phoezelle/puddingplayer/src/ofApp.cpp

#include "ofApp.h"
#include "wiringPi.h"
#include <wiringPiSPI.h>
#include <cstdlib>
#include <iostream>
#include <sstream>
#include <string>
#include <unistd.h>



void ofApp::log(string log,int level,bool color){
  if(level<=loglevel){
    if(color) cout << "\033[32m";
    if(level==WARNING) cout << "\x1b[31m";
    cout << log;
    if(color || level==WARNING) cout << "\x1b[0m";
    cout << endl;
    if(level<=USR)firstMessage+=log+"\n";
  }
}



void ofApp::definePlateform(){
  ofTargetPlatform myRun = ofGetTargetPlatform();
  if (myRun==OF_TARGET_LINUXARMV7L || myRun==OF_TARGET_LINUXARMV6L){
    pi=true;
    fingerMovie->setPixelFormat(OF_PIXELS_NATIVE);
    fingerMovie2->setPixelFormat(OF_PIXELS_NATIVE);
    rootDirectory="/tmp/stick";
    log("RASPI DETECT path from usb stick", USR);
    
  } else {
    pi=false;
    rootDirectory="";
    log("MAC DETECT", USR);
    
  }
}

void ofApp::usbstickMount(){
  ofDirectory myDir;
  if(myDir.doesDirectoryExist(rootDirectory)){
  } else {
    ofSystem("sudo mkdir "+rootDirectory);
    log("create mountpoint "+rootDirectory, USR);
  }
  if (myDir.listDir(rootDirectory)>1) {
    log("USB stick already mount", USR);
    flash_ledG(1);
  } else {
    ofSystem("sudo mount -o rw /dev/sda1 "+rootDirectory);
    if(myDir.listDir(rootDirectory)>1) {
      log("mount usb stick", USR);
      flash_ledG(1);
    }else {
      log("problem for mounting usb stick", WARNING);
      flash_ledR(1);
    }
  }
  rootDirectory+="/";
}



//--------------------------------------------------------------
void ofApp::setup(){
  
  ledG_value = 0;
  ledG_state = 0;
  ledG_time_on = ofGetElapsedTimeMillis();
  ledG_time_period = 50;
  
  ledR_state = 0;
  ledR_value = 0;
  ledR_time_on = ofGetElapsedTimeMillis();
  ledR_time_period = 200;
  
  nvideo=0;
  gochangevideo=0;
  isplayground=true;
  
  
  firstlaunch=true;
  loglevel=USR;
  pi=true;
  currentVideo=-1;
  currentScene=0;
  currentBackground=0;
  
  log("STARTUP",USR,true);
  
  ofHideCursor();
  ofBackground(0,0,0);
	ofSetVerticalSync(true);
  
  fingerMovie = new ofVideoPlayer();
  fingerMovie2 = new ofVideoPlayer();
  
  definePlateform();
  if (pi) {
    usbstickMount();
    initGPIO();
    
    
  }
  ofBackground(0,0,0);
  getPref();
  setcurrentCharacter(0);
  checkNetwork();
  
  thread.startThread(true);
  
  playBackground();
  
	// Uncomment this to show movies with alpha channels
	// fingerMovie.setPixelFormat(OF_PIXELS_RGBA);
  
}


void ofApp::getPref(){
  
  posX=0;
  posY=0;
  width=ofGetScreenWidth();
  height=ofGetScreenHeight();
  log("screen size "+ofToString(ofGetWindowWidth())+" x "+ofToString(ofGetWindowHeight())+" / "+ofToString(ofGetScreenWidth())+" x "+ofToString(ofGetScreenHeight()),USR);
  loglevel=DEBUG;
  
  ofBuffer buffer = ofBufferFromFile(rootDirectory+"config.txt");
	if(buffer.size()) {
    for (ofBuffer::Line it = buffer.getLines().begin(), end = buffer.getLines().end(); it != end; ++it) {
      string line = *it;
      if(line.empty() == false) {
        string attribute = ofTrim(ofSplitString(line, "=")[0]);
        string value = ofTrim(ofSplitString(line, "=")[1]);
        
        if (attribute.compare("positionX")==0) posX=ofToInt(value);
        if (attribute.compare("positionY")==0) posY=ofToInt(value);
        if (attribute.compare("largeur")==0) width=ofToInt(value);
        if (attribute.compare("hauteur")==0) height=ofToInt(value);
        if (attribute.compare("loglevel")==0) loglevel=ofToInt(value);
        if (attribute.compare("dossier_personnage")==0) characterList =  ofSplitString(value, ",");
        if (attribute.compare("dossier_background")==0) backgroundDirectory = value;
        log("read param "+attribute+" = "+value, DEBUG);
      }else {
        break;
      }
    }
	}else{
    log(rootDirectory+"config.txt file not found",WARNING);
    flash_ledR(2);
  }
  
  ofSetWindowShape(width, height);
}


void ofApp::setcurrentCharacter(int _character){
  currentCharacter = _character;
  log("set character n" + ofToString(currentCharacter) + " -> directory " + characterList[currentCharacter], USR);
  buildMediaList();
}


void ofApp::buildMediaList(){
  log("Build media list",USR);
  mediaList.clear();
  ofDirectory myDir;
  if(!myDir.doesDirectoryExist(rootDirectory+"movies")){
    ofSystem("sudo mkdir "+rootDirectory+"movies");
    log("create movies directory", USR,true);
  }
  mediaDirectory = "movies/"+characterList[currentCharacter];
  if(!myDir.doesDirectoryExist(rootDirectory+mediaDirectory)){
    ofSystem("sudo mkdir "+rootDirectory+mediaDirectory);
    log("create " + mediaDirectory + " directory", USR,true);
  }
  ofDirectory mediaDir(rootDirectory+mediaDirectory);
  mediaDir.allowExt("mp4");
  mediaDir.allowExt("mov");
  mediaDir.allowExt("avi");
  nbMedia = mediaDir.listDir();
  mediaDir.sort();
  int lastScene=-1;
  vector <string> scene;
  if (nbMedia>0) {
    log("find " + ofToString(nbMedia) + " movie files in " + mediaDirectory,DEBUG);
    for (int i=0; i<nbMedia; i++) {
      string media = mediaDir.getName(i);
      
      int numScene = ofToInt(ofTrim(ofSplitString(media, "_")[0]));
      if(lastScene == -1) lastScene = numScene;
      int numVideo = ofToInt(ofTrim(ofSplitString(media, "_")[1]));
      if(numScene != lastScene) {
        log("new scene",DEBUG);
        lastScene = numScene;
        mediaList.push_back(scene);
        scene.clear();
      }
      log(media,DEBUG);
      scene.push_back(media);
    }
    mediaList.push_back(scene);
  }else{
    log("no media found in " + mediaDirectory,WARNING);
  }
  
  
  ofDirectory backgroundDir(rootDirectory+mediaDirectory+"/"+backgroundDirectory);
  backgroundDir.allowExt("mp4");
  backgroundDir.allowExt("mov");
  backgroundDir.allowExt("avi");
  int nbBackground = backgroundDir.listDir();
  if (nbBackground>0) {
    log("find " + ofToString(nbBackground) + " background movie files in " + mediaDirectory+"/"+backgroundDirectory,DEBUG);
    for (int i=0; i<nbBackground; i++) {
      string media = backgroundDir.getName(i);
      backgroundList.push_back(media);
    }
  }else{
    log("no background media found in " + mediaDirectory+"/"+backgroundDirectory,WARNING);
  }
}

void ofApp::checkNetwork(){
  cout << "checking network";
  if(pi) {
    string ip_eth = ofTrim(ofSystem("ifconfig eth0 | grep 'inet addr:' | cut -d: -f2 | awk '{ print $1}'"));
    string ip_wlan = ofTrim(ofSystem("ifconfig wlan0 | grep 'inet addr:' | cut -d: -f2 | awk '{ print $1}'"));
    string hostname = ofTrim(ofSystem("cat /etc/hostname"));
    log("network on pi name "+hostname+" : eth "+ip_eth+" ; wlan "+ip_wlan, USR);
  }else {
    string ip_en1 = ofSystem("ifconfig en1 | grep 'inet ' | cut -dt -f2 | awk '{ print $1}'");
    log("network on mac : en1 "+ip_en1, USR);
  }
}


void ofApp::initGPIO(){
  
  pin[0] = PUSH1;
  pin[1] = PUSH2;
  pin[2] = PUSH3;
  
  if(wiringPiSetup() == -1){
    log("Error on wiringPi setup\n",WARNING);
  }else {
    log("configure GPIO IN", USR);
    for (int i=0; i<PIN_NUM; i++) {
      pinMode(pin[i],INPUT);
      pullUpDnControl(pin[i],PUD_DOWN);
      log("read initial state of pin", USR);
      laststate[i]=digitalRead(pin[i]);
    }
    delay(1);
    log("configure GPIO OUT", USR);
    pinMode(LEDR,OUTPUT);
    pinMode(LEDG,OUTPUT);
    
  }
  
  log("wait for RF24 config", USR);
  while (1){
    string input;
    getline(cin, input);
    if(input.length()>3){
      log("cin = "+input, USR);
      if (input.compare("INITEND")==0) break;
    }
  }
  
  
}

void ofApp::getAnalogBattery(){
  
}


void ofApp::playNext(){
  if (currentVideo==-1){
    log("first time play",DEBUG);
    currentVideo=0;
    isplayground=false;
    play();
    return;
  }
  if (mediaList[currentScene][currentVideo] == mediaList.back().back()) {
    log("return to first scene",DEBUG);
    currentScene=0;currentVideo=0;
  }else{
    if(mediaList[currentScene][currentVideo] == mediaList[currentScene].back()) {
      log("go next scene",DEBUG);
      currentScene++;currentVideo=0;
    }else{
      log("go next video",DEBUG);
      currentVideo++;
    }
  }
  isplayground=false;
  play();
}

void ofApp::play(){
  gochangevideo=1;
  flash_ledG(1);
  string videoPath="";
  if(isplayground){
    videoPath = rootDirectory+mediaDirectory+"/"+backgroundDirectory+"/"+ backgroundList[currentBackground];
    log("play backgroung video "+videoPath, USR);
  } else {
    videoPath = rootDirectory+mediaDirectory+"/"+ mediaList[currentScene][currentVideo];
    log("play video ("+ofToString(currentScene)+"/"+ofToString(currentVideo)+") "+videoPath, USR,true);
  }
  
  if(nvideo==0){
    //log("delete video2",USR);
    //delete fingerMovie;
    //log("create video2",USR);
    //fingerMovie2 = new ofVideoPlayer();
    fingerMovie2->setPixelFormat(OF_PIXELS_NATIVE);
    fingerMovie2->setLoopState(OF_LOOP_NONE);
    log("load video2",USR);
    fingerMovie2->loadAsync(videoPath);
  }
  
  if(nvideo==1){
    //log("delete video1",USR);
    //delete fingerMovie;
    //log("create video1",USR);
    //fingerMovie = new ofVideoPlayer();
    fingerMovie->setPixelFormat(OF_PIXELS_NATIVE);
    fingerMovie->setLoopState(OF_LOOP_NONE);
    log("load video1",USR);
    fingerMovie->loadAsync(videoPath);
  }
}

void ofApp::clearVideo(int n){
  if (n==0 && fingerMovie!=nullptr) {
    if(fingerMovie->isPlaying()){
      log("stop previous video1",USR);
      fingerMovie->stop();
      delay(10);
    }
    //log("close previous video1",USR);
    //fingerMovie->close();
  }
  if (n==1 && fingerMovie2!=nullptr) {
    if(fingerMovie2->isPlaying()){
      log("stop previous video2",USR);
      fingerMovie2->stop();
      delay(10);
    }
    //log("close previous video2",USR);
    //fingerMovie2->close();
  }
}

void ofApp::pausePlay(){
  log("play/pause video ", USR);
  if(nvideo==0)fingerMovie->setPaused(!fingerMovie->isPaused());
  if(nvideo==1)fingerMovie2->setPaused(!fingerMovie2->isPaused());
}

void ofApp::playBackground(){
  isplayground=true;
  play();
}

void ofApp::changeBackground(){
  log("change background ", USR);
  if(backgroundList[currentBackground]==backgroundList.back()){
    currentBackground=0;
  } else {
    currentBackground++;
  }
}

void ofApp::nextScene(){
  if(mediaList[currentScene][currentVideo] != mediaList.back()[currentVideo]){
    log("go next scene ", USR);
    currentVideo=0;
    currentScene++;
    play();
  }else{
    log("no next scene ", USR);
  }
}

void ofApp::restartScene(){
  log("restart scene ", USR);
  currentVideo=0;
  play();
  
}


void ofApp::checkGPIO(){
  for (int i=0; i<PIN_NUM; i++) {
    int gpio_state = digitalRead(pin[i]);
    if(gpio_state!=laststate[i]){
      laststate[i]=gpio_state;
      if (gpio_state==0) {
        if(!longpush[i]){
          log("short push release wiring pi "+ofToString(pin[i]), DEBUG);
          
          if(i==0){
            playNext();
          }
          if(i==1){
            pausePlay();
          }
          if(i==2){
            nextScene();
          }
        }else{
          log("long push release wiring pi "+ofToString(pin[i]), DEBUG);
          
          if(i==1){
            changeBackground();
          }
          if(i==2){
            restartScene();
          }
        }
      }else{
        log("push up wiring pi "+ofToString(pin[i]), DEBUG);
        startpushtime[i]=ofGetElapsedTimeMillis();
      }
      longpush[i]=false;
      
    }
    if(gpio_state!=0 && !longpush[i] && ofGetElapsedTimeMillis() - startpushtime[i] > 3000){
      longpush[i]=true;
      log("longmode wiring pi "+ofToString(pin[i]), DEBUG);
    }
    
  }
}



void ofApp::checkREMOTE(){
  int myorder=0;
  thread.lock();
  myorder=thread.order;
  thread.order=0;
  thread.unlock();
  if (myorder > 0){
    thread.order=0;
    log("get order"+ofToString(myorder),USR);
    flash_ledR(1);
    switch (myorder) {
      case 1:
        playNext();
        break;
      case 2:
        playNext();
        break;
      case 3:
        pausePlay();
        break;
      case 4:
        changeBackground();
        break;
      case 5:
        nextScene();
        break;
      case 6:
        restartScene();
        break;
      case 8:
        system ("sudo reboot");
        break;
      default:
        break;
    }
  }
}


void ofApp::checkLed(){
  
  if(ledR_state > 0 && ofGetElapsedTimeMillis() - ledR_time_on > ledR_time_period){
    //Serial.print("led");Serial.print(ledR_state,DEC);Serial.print("-");Serial.print(ledR_value,DEC);
    ledR_time_on = ofGetElapsedTimeMillis();
    ledR_state--;
    if(ledR_value == 1) ledR_value=0; else ledR_value=1;
    digitalWrite(LEDR, ledR_value);
  }
  if(ledR_state==0){
    ledR_value=0;
    digitalWrite(LEDR, ledR_value);
  }
  
  if(ledG_state > 0 && ofGetElapsedTimeMillis()- ledG_time_on > ledG_time_period){
    //Serial.print("led");Serial.print(ledR_state,DEC);Serial.print("-");Serial.print(ledR_value,DEC);
    ledG_time_on = ofGetElapsedTimeMillis();
    ledG_state--;
    if(ledG_value == 1) ledG_value=0; else ledG_value=1;
    digitalWrite(LEDG, ledG_value);
  }
  if(ledG_state==0){
    ledG_value=0;
    digitalWrite(LEDG, ledG_value);
  }
}

void ofApp::flash_ledG(int f){
  log("flash G "+ofToString(f),USR);
  ledG_state=2*f;
}

void ofApp::flash_ledR(int f){
  log("flash R "+ofToString(f),USR);
  ledR_state=2*f;
}


//--------------------------------------------------------------
void ofApp::update(){
  if(fingerMovie!=nullptr)fingerMovie->update();
  if(fingerMovie2!=nullptr)fingerMovie2->update();
  if(pi)checkGPIO();
  if(pi)checkREMOTE();
  if(pi)checkLed();
}

//--------------------------------------------------------------
void ofApp::draw(){
  //checkinputandplayVideo();
  
	ofSetHexColor(0xFFFFFF);
  
  if(nvideo==0 && gochangevideo==1){
    if(fingerMovie2->isLoaded()){
    log("start play video 2", USR);
    fingerMovie2->play();
    gochangevideo=2;
    }
  }
  if(nvideo==1 && gochangevideo==1){
    if(fingerMovie->isLoaded()){
    log("start play video 1", USR);
    fingerMovie->play();
    gochangevideo=2;
    }
  }
  
  if(nvideo==0 && gochangevideo==2){
    if(fingerMovie2->isFrameNew()){
    log("switch from video 1 to 2", USR);
    clearVideo(nvideo);
    gochangevideo=0;
    nvideo=1;
    log("video1 is stop", USR);
    }
  }
  if(nvideo==1 && gochangevideo==2){
    if(fingerMovie->isFrameNew()){
    log("switch from video 2 to 1", USR);
    clearVideo(nvideo);
    gochangevideo=0;
    nvideo=0;
    log("video2 is stop", USR);
    }
  }

  
  if(nvideo==0) fingerMovie->draw(posX,posY,width,height);
  if(nvideo==1) fingerMovie2->draw(posX,posY,width,height);
  ofSetHexColor(0xff3300);
  
  if(ofGetElapsedTimeMillis()<60000){
    ofDrawBitmapString(firstMessage,100,420);
  }
  
  if(nvideo==0 && gochangevideo==0){
    if(fingerMovie->getIsMovieDone()){
      log("end video",DEBUG);
      playBackground();
    }
  }
  if(nvideo==1 && gochangevideo==0){
    if(fingerMovie2->getIsMovieDone()){
      log("end video",DEBUG);
      playBackground();
    }
  }
}







//--------------------------------------------------------------
void ofApp::keyPressed  (int key){
  switch(key){
    case 'a':
      playNext();
      break;
    case 'b':
      playBackground();
      break;
    case 'c':
      changeBackground();
      break;
    case 'p':
      pausePlay();
      break;
    case 's':
      nextScene();
      break;
    case 'r':
      restartScene();
      break;
      
      
  }
  
}

//--------------------------------------------------------------
void ofApp::keyReleased(int key){
  
}

//--------------------------------------------------------------
void ofApp::mouseMoved(int x, int y ){
  
}

//--------------------------------------------------------------
void ofApp::mouseDragged(int x, int y, int button){
  
}

//--------------------------------------------------------------
void ofApp::mousePressed(int x, int y, int button){
  
}


//--------------------------------------------------------------
void ofApp::mouseReleased(int x, int y, int button){
  
}

//--------------------------------------------------------------
void ofApp::mouseEntered(int x, int y){
  
}

//--------------------------------------------------------------
void ofApp::mouseExited(int x, int y){
  
}

//--------------------------------------------------------------
void ofApp::windowResized(int w, int h){
  
}

//--------------------------------------------------------------
void ofApp::gotMessage(ofMessage msg){
  
}

//--------------------------------------------------------------
void ofApp::dragEvent(ofDragInfo dragInfo){
  
}

void ofApp::exit() {
  // stop the thread
  thread.stopThread();
}


/*
 void ofApp::checkinputandplayVideo(){
 if(firstlaunch){
 lastpath="inconnu";
 if (!fingerMovie.isPlaying()){
 playVideoInPath();
 }
 firstlaunch=false;
 }
 }
 
 void ofApp::playVideoInPath() {
 ofDirectory myDir;
 if(myDir.doesDirectoryExist(rootDirectory+"movies/"+ lastpath)){
 int maxVideo = myDir.listDir(rootDirectory+"movies/" + lastpath);
 cout << ofToString(maxVideo) << " files in path : " << rootDirectory << "movies/" << lastpath <<  endl;
 int selected = (int) ofRandom(maxVideo);
 cout << "\x1b[32mtry read video "<< selected << " : " << myDir.getPath(selected) << "\x1b[0m" << endl;
 
 fingerMovie.load(myDir.getPath(selected));
 fingerMovie.setLoopState(OF_LOOP_NONE);
 // cout << "video size" << fingerMovie.getHeight() << "/" << fingerMovie.getWidth() << endl;
 fingerMovie.play();
 
 }
 }
 */
